Keyaan-07/mmWave/cart.png

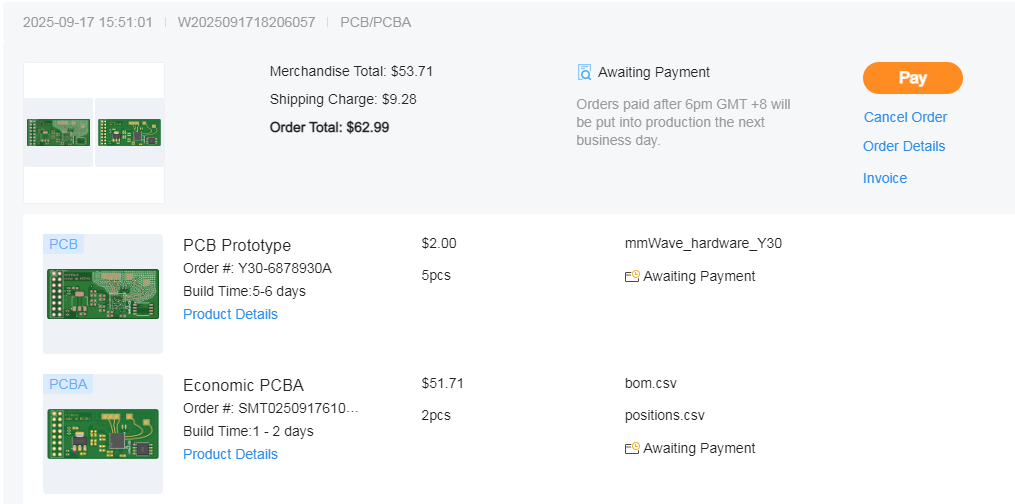
cart.png
