Keyaan-07/mmWave/images/aug10/starting!.png

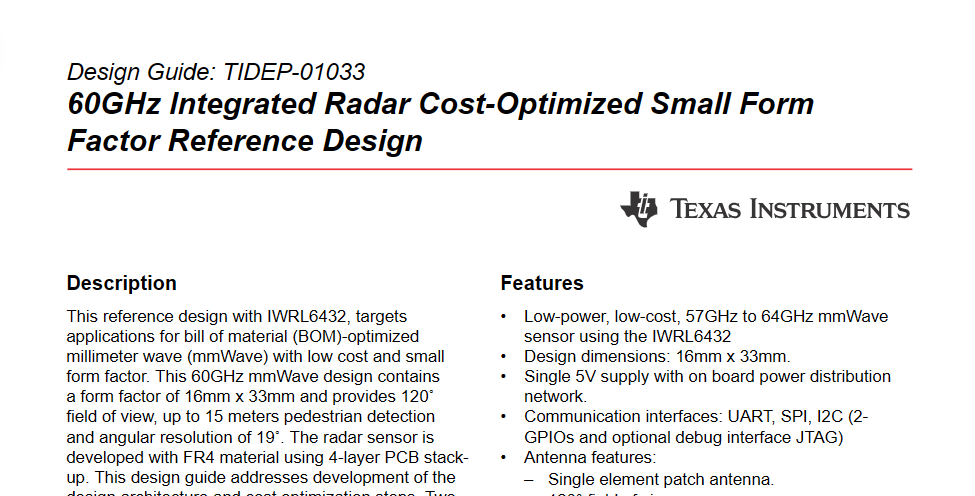
images/aug10/starting!.png
